stromberg-DS/SmartPlant/Images/IMG_2785.jpeg

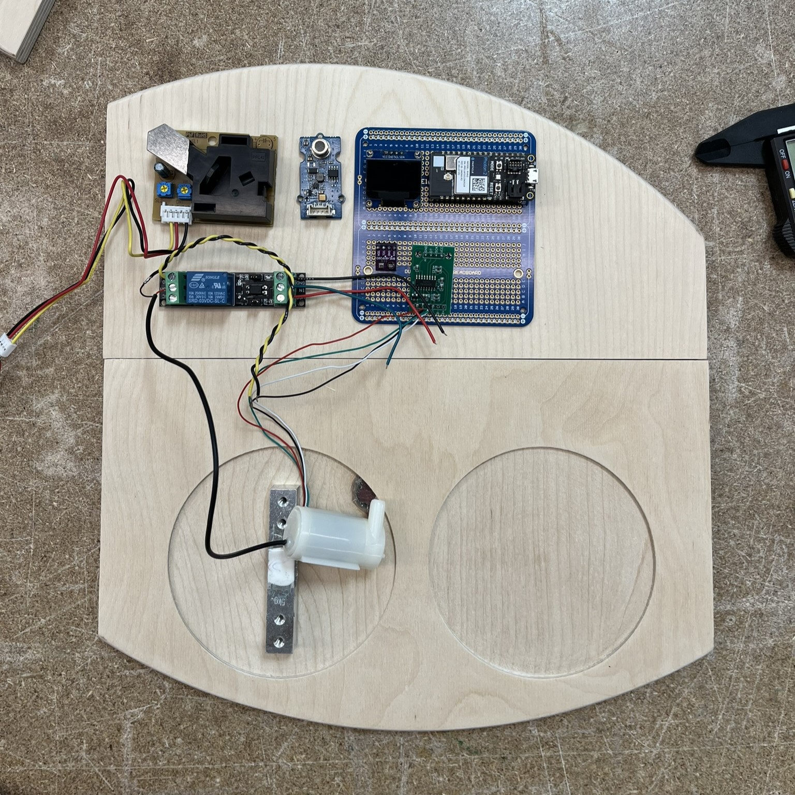
Images/IMG_2785.jpeg
