stromberg-DS/SmartPlant/Images/IMG_2786.jpeg

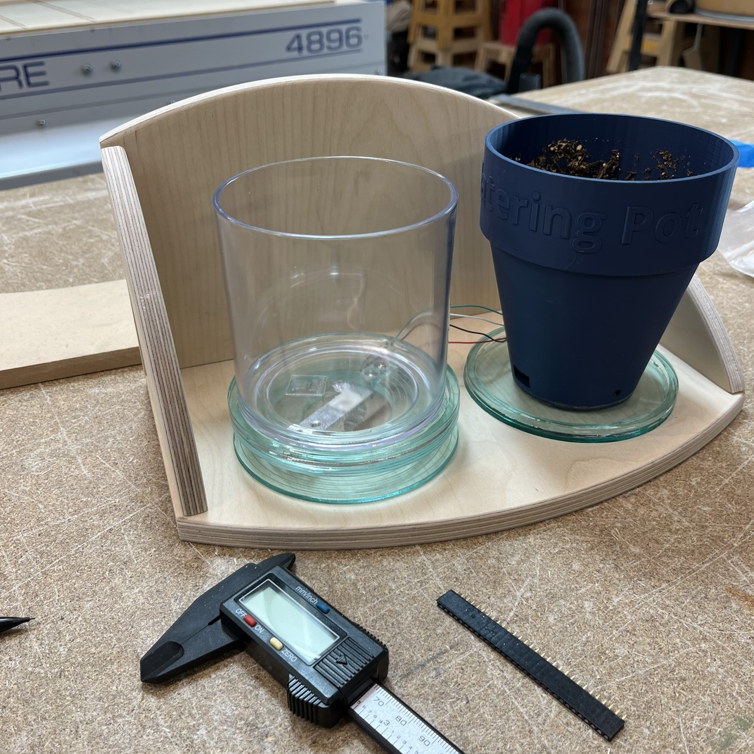
Images/IMG_2786.jpeg
