stromberg-DS/SmartPlant/Images/IMG_2793.jpeg

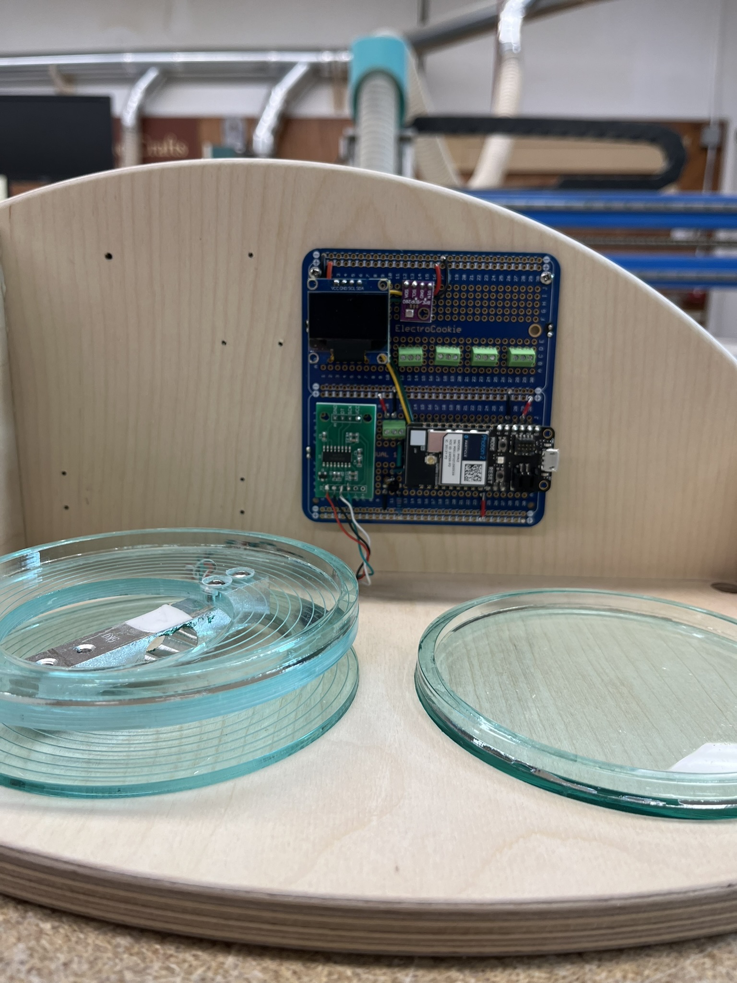
Images/IMG_2793.jpeg
