stromberg-DS/SmartPlant/Images/IMG_2814.jpeg

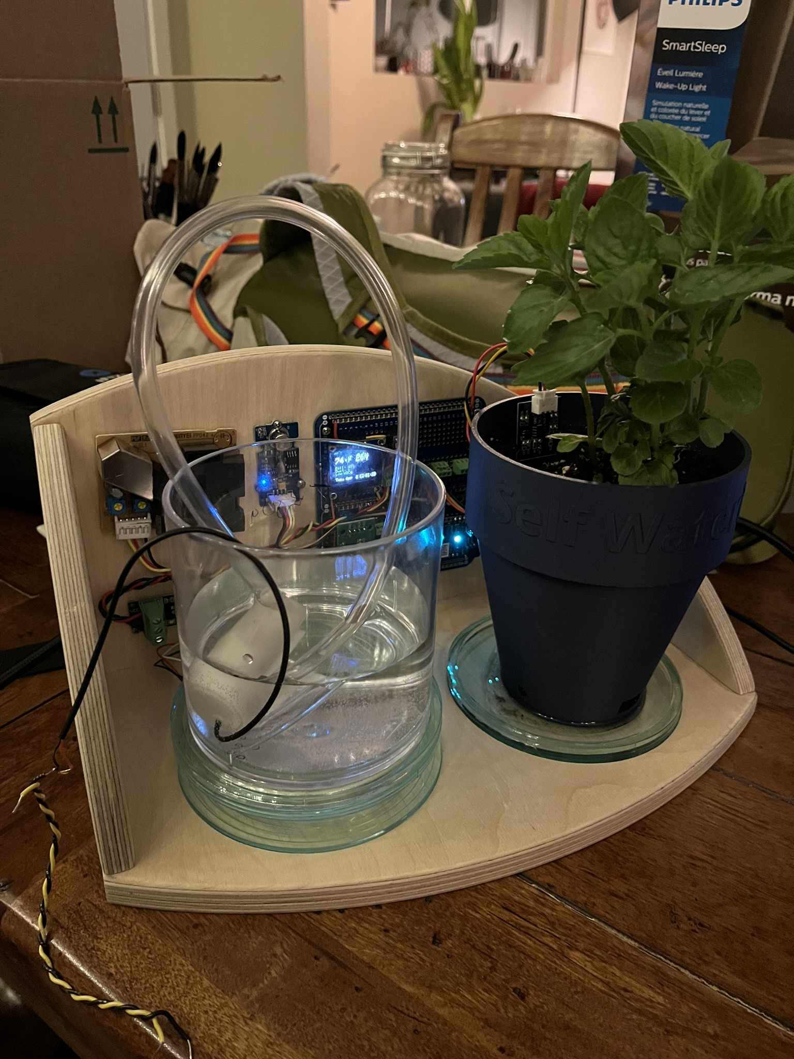
Images/IMG_2814.jpeg
